AdryRocha/medical-clinic-checkin/config/wifi_config.hpp

#ifndef WIFI_CONFIG_HPP
#define WIFI_CONFIG_HPP

/**
 * @file wifi_config.hpp
 * @brief WiFi configuration
 */

// ============================================================================
// WiFi Network Credentials (TESTING!)
// ============================================================================
#define WIFI_SSID           ""
#define WIFI_PASSWORD       ""

// ============================================================================
// WiFi Core Settings
// ============================================================================
#define WIFI_COUNTRY_CODE   "BR"
#define WIFI_CONNECT_TIMEOUT_MS 30000

#endif // WIFI_CONFIG_HPP
