AdryRocha/medical-clinic-checkin/src/ui/screens/init_status_screen.hpp

#ifndef INIT_STATUS_SCREEN_HPP
#define INIT_STATUS_SCREEN_HPP

void init_status_screen_show(const char* title, const char* message);
void init_status_screen_update(const char* title, const char* message);

#endif
