AdryRocha/medical-clinic-checkin/src/ui/screens/welcome_screen.hpp

#ifndef WELCOME_SCREEN_HPP
#define WELCOME_SCREEN_HPP

void welcome_screen_show(const char* msg = nullptr);
void welcome_screen_update(const char* msg = nullptr);
void welcome_screen_update_time();

#endif
